vankxr/hdd-booster/pcb/hdd-booster-bot.png

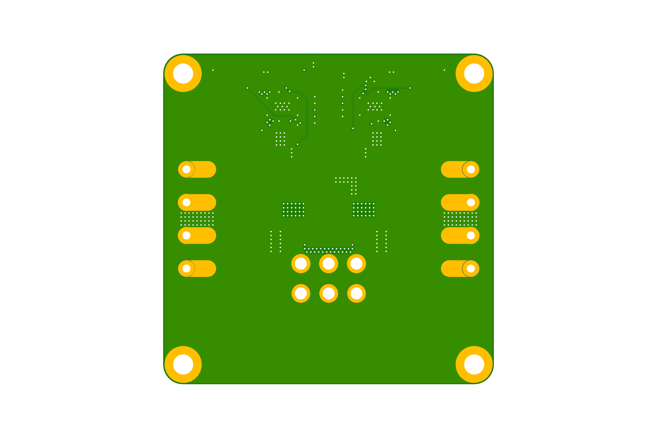
pcb/hdd-booster-bot.png
